SergioGasquez/Open_Grips/prometheus-fit/examples/right-hand/prometheus_right_pinky_roller.stl

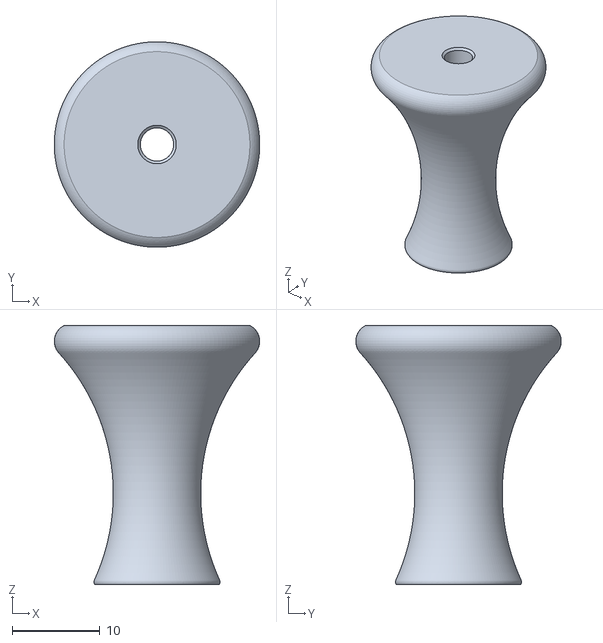
[picture p15: CAD file, 2026-10-08]
prometheus-fit/examples/right-hand/prometheus_right_pinky_roller.stl
23.5 x 23.5 x 29.6
